AriaSalvatrice/synth-protoboard/Half-Protoboard.kicad_sch

## KiCad design Half-Protoboard.kicad_sch (2023-03-09)

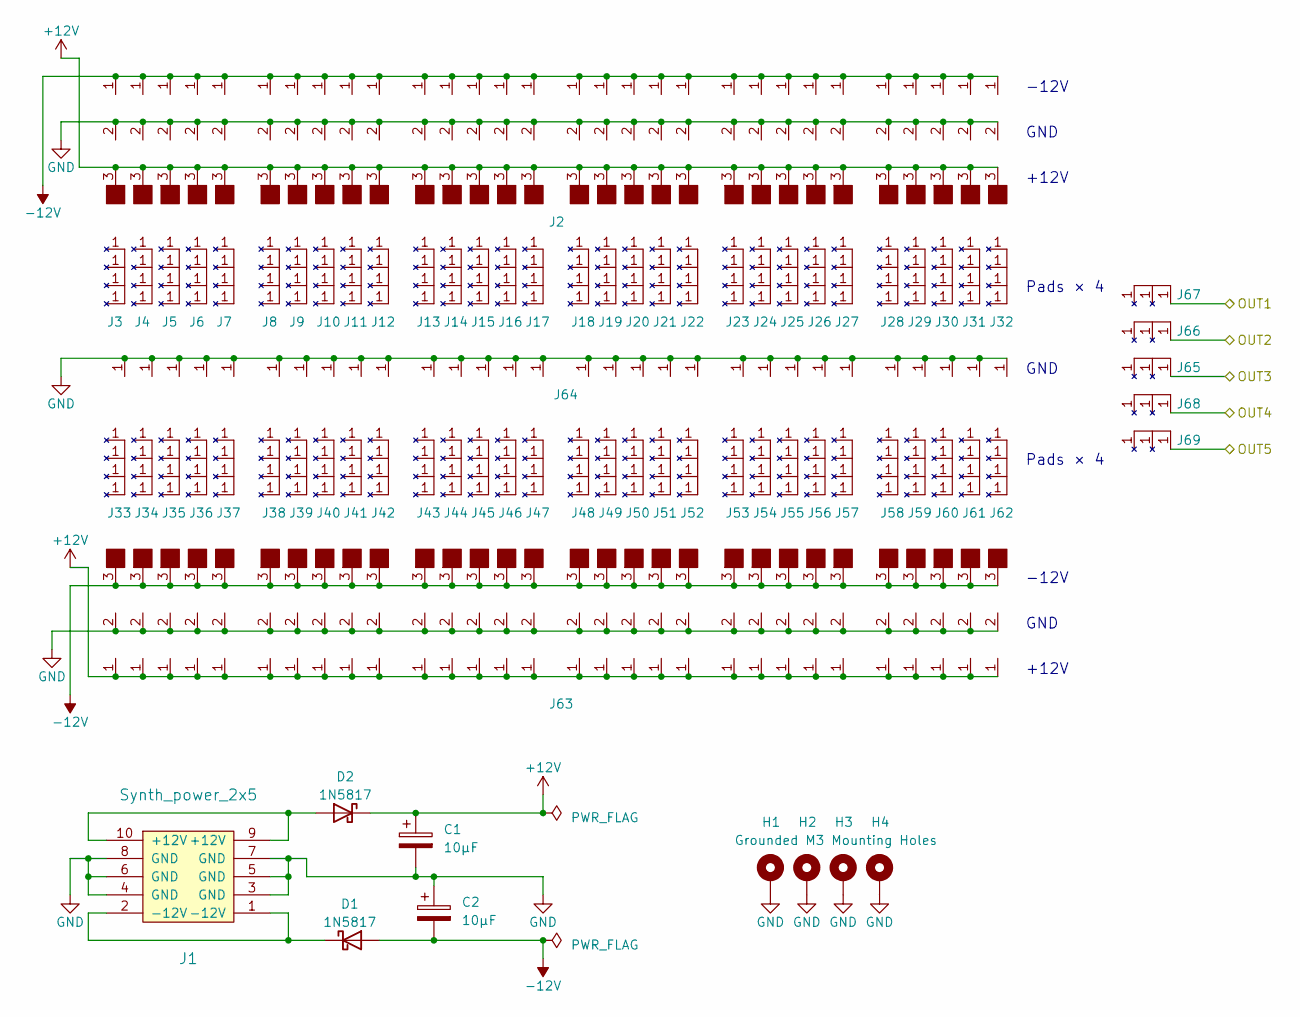
[picture p8: schematic Half-Protoboard.kicad_sch]

Parts:
C1, C2: 10µF; CP_Radial_D6.3mm_P2.50mm
D1, D2: 1N5817; D_DO-41_SOD81_P10.16mm_Horizontal
H1: Grounded M3 Mounting Holes; MountingHole_3.2mm_M3_Pad_Via
H2, H3, H4: MountingHole_Pad; MountingHole_3.2mm_M3_Pad_Via
J1: Synth_power_2x5; Power_Header
J2, J63: Power_Rail_Bipolar_30
J3, J4, J5, J6, J7, J8, J9, J10, J11, J12, J13, J14, J15, J16, J17, J18, J19, J20, J21, J22, J23, J24, J25, J26, J27, J28, J29, J30, J31, J32, J33, J34, J35, J36, J37, J38, J39, J40, J41, J42, J43, J44, J45, J46, J47, J48, J49, J50, J51, J52, J53, J54, J55, J56, J57, J58, J59, J60, J61, J62: Connectable_Pad_Group_01x04
J64: Ground_Rail_30; Ground_Rail_Double_Size_30
J65, J66, J67, J68, J69: Connectable_Pad_Group_01x03

Connections:
+12V: C1.1, D2.1 (K), J2.3, J63.1
-12V: C2.2, D1.2 (A), J2.1, J63.3
GND: C1.2, C2.1, H1.1, H2.1, H3.1, H4.1, J1.3 (GND), J1.4 (GND), J1.5 (GND), J1.6 (GND), J1.7 (GND), J1.8 (GND), J2.2, J63.2, J64.1
unnamed: D1.1 (K), J1.1 (-12V), J1.2 (-12V)
unnamed: D2.2 (A), J1.9 (+12V), J1.10 (+12V)
OUT1: J67.1
OUT2: J66.1
OUT3: J65.1
OUT4: J68.1
OUT5: J69.1

Notes on the sheet:
Pads × 4
-12V
GND
+12V
